okyeron/shieldXL/enclosure/shieldXL_case_v1.5.1-SLS-Nylon/shieldXL_case_jp_v1.5.1.step

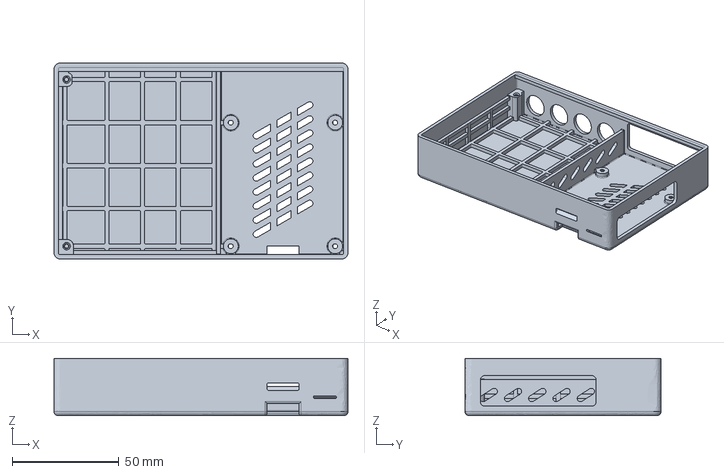
[picture p21: CAD file, 2023-10-02, an earlier design]
enclosure/shieldXL_case_v1.5.1-SLS-Nylon/shieldXL_case_jp_v1.5.1.step
138.0 x 92.0 x 26.9 mm
